alterscape/SimulatorCollectiveFirmware/CollectiveButtonBox/ShiftToButtons.cpp

#include "ShiftToButtons.h"


ShiftButtons::ShiftButtons()
{
  pinValues = 0;
  oldPinValues = 1;
}

void ShiftButtons::setup()
{
   /* Initialize our digital pins...
    */
    pinMode(ploadPin, OUTPUT);
    pinMode(clockEnablePin, OUTPUT);
    pinMode(clockPin, OUTPUT);
    pinMode(dataPin, INPUT);

    digitalWrite(clockPin, LOW);
    digitalWrite(ploadPin, HIGH);

    /* Read in and display the pin states at startup.
    */
    pinValues = read_shift_regs();
    display_pin_values();
    oldPinValues = pinValues;
}

BYTES_VAL_T ShiftButtons::read_shift_regs()
{
  long bitVal;
  BYTES_VAL_T bytesVal = 0;

  /* Trigger a parallel Load to latch the state of the data lines,
  */
  digitalWrite(clockEnablePin, HIGH);
  digitalWrite(ploadPin, LOW);
  delayMicroseconds(PULSE_WIDTH_USEC);
  digitalWrite(ploadPin, HIGH);
  digitalWrite(clockEnablePin, LOW);

  /* Loop to read each bit value from the serial out line
     of the SN74HC165N.
  */
  for (int i = 0; i < DATA_WIDTH; i++)
  {
    bitVal = digitalRead(dataPin);

    /* Set the corresponding bit in bytesVal.
    */
    bytesVal |= (bitVal << ((DATA_WIDTH - 1) - i));

    /* Pulse the Clock (rising edge shifts the next bit).
    */
    digitalWrite(clockPin, HIGH);
    delayMicroseconds(PULSE_WIDTH_USEC);
    digitalWrite(clockPin, LOW);
  }

  return (bytesVal);
}


void ShiftButtons::display_pin_values()
{
  Serial.print("Pin States:\r\n");

  for (int i = 0; i < DATA_WIDTH; i++)
  {
    Serial.print("  Pin-");
    Serial.print(i);
    Serial.print(": ");

    if ((pinValues >> i) & 1)
      Serial.print("HIGH");
    else
      Serial.print("LOW");

    Serial.print("\r\n");
  }

  Serial.print("\r\n");
}
